esteban-andrade/AutonomousFireDataCollect/flir_one_node/demo/Screenshot from 2021-02-14 20-05-26.png

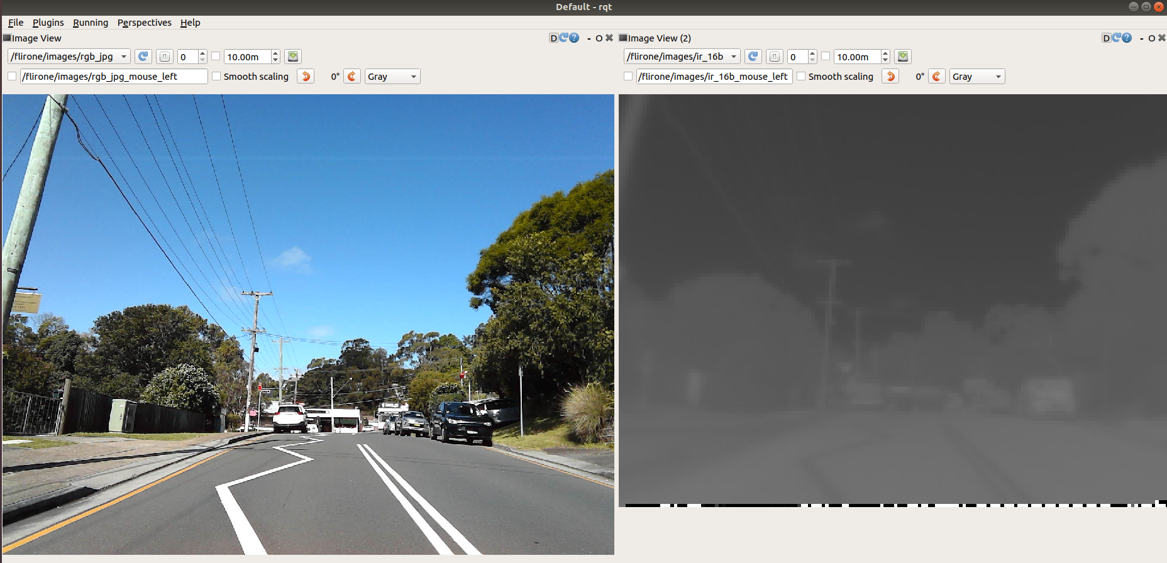
flir_one_node/demo/Screenshot from 2021-02-14 20-05-26.png
