esteban-andrade/AutonomousFireDataCollect/flir_one_node/demo/Screenshot from 2021-02-15 16-28-25.png

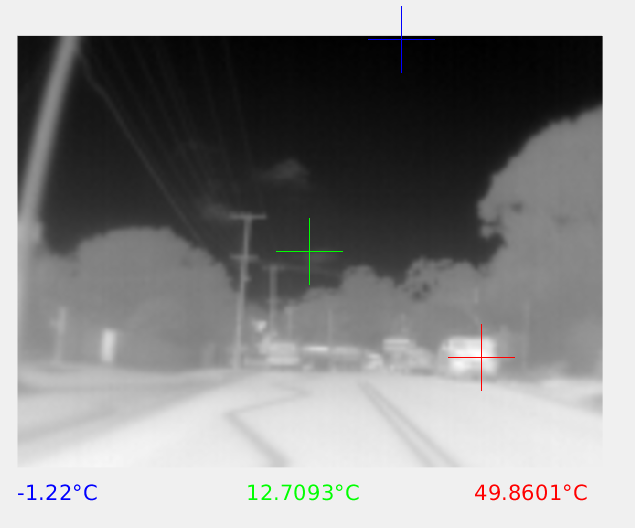
flir_one_node/demo/Screenshot from 2021-02-15 16-28-25.png
