esteban-andrade/AutonomousFireDataCollect/flir_one_node/demo/Screenshot from 2021-02-15 16-32-08.png

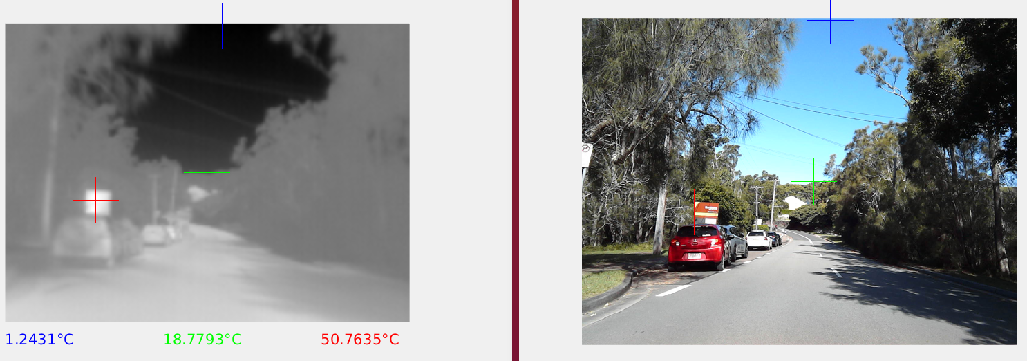
flir_one_node/demo/Screenshot from 2021-02-15 16-32-08.png
