esteban-andrade/AutonomousFireDataCollect/flir_one_node/demo/Screenshot from 2021-02-16 15-38-59.png

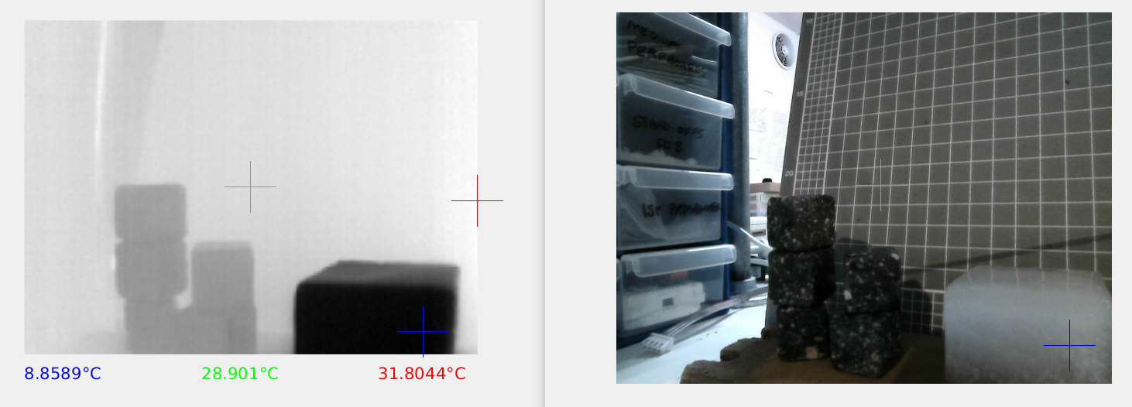
flir_one_node/demo/Screenshot from 2021-02-16 15-38-59.png
