esteban-andrade/AutonomousFireDataCollect/flir_one_node/demo/Screenshot from 2021-02-16 15-42-15.png

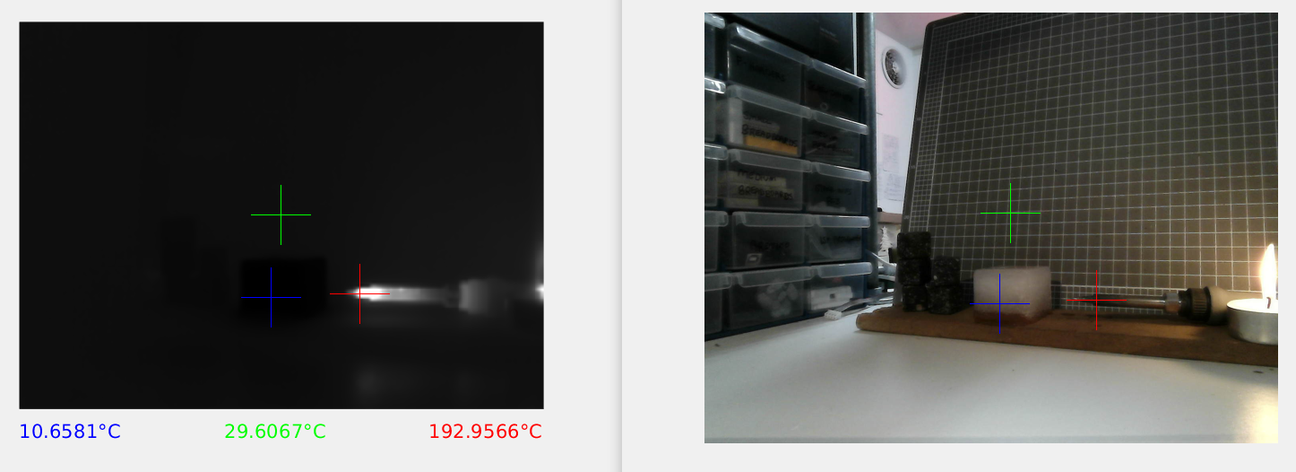
flir_one_node/demo/Screenshot from 2021-02-16 15-42-15.png
