esteban-andrade/AutonomousFireDataCollect/flir_one_node/demo/Screenshot from 2021-02-16 16-03-48.png

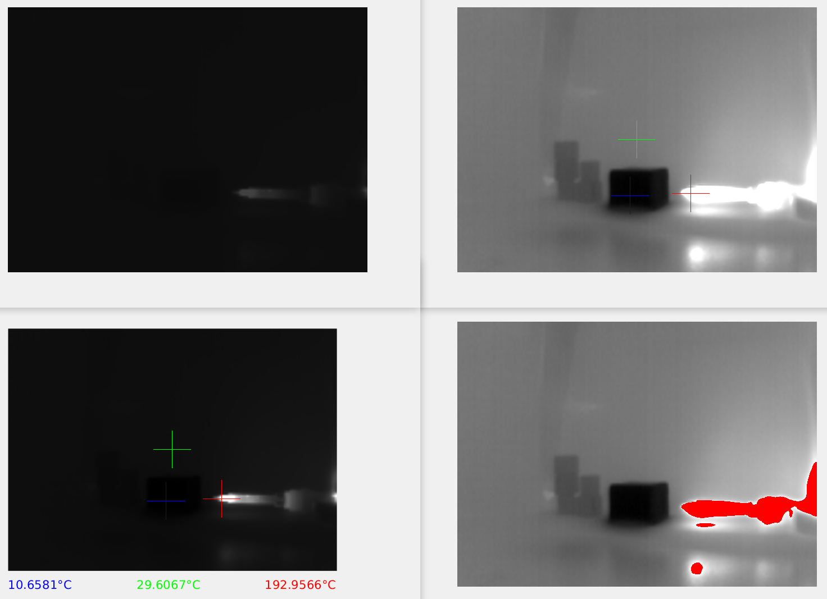
flir_one_node/demo/Screenshot from 2021-02-16 16-03-48.png
