esteban-andrade/AutonomousFireDataCollect/flir_one_node/v4l2loopback/new2.png

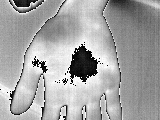
flir_one_node/v4l2loopback/new2.png
