esteban-andrade/AutonomousFireDataCollect/flir_one_node/v4l2loopback/new.png

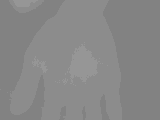
flir_one_node/v4l2loopback/new.png
