esteban-andrade/AutonomousFireDataCollect/flir_one_node/v4l2loopback/rgb.jpg

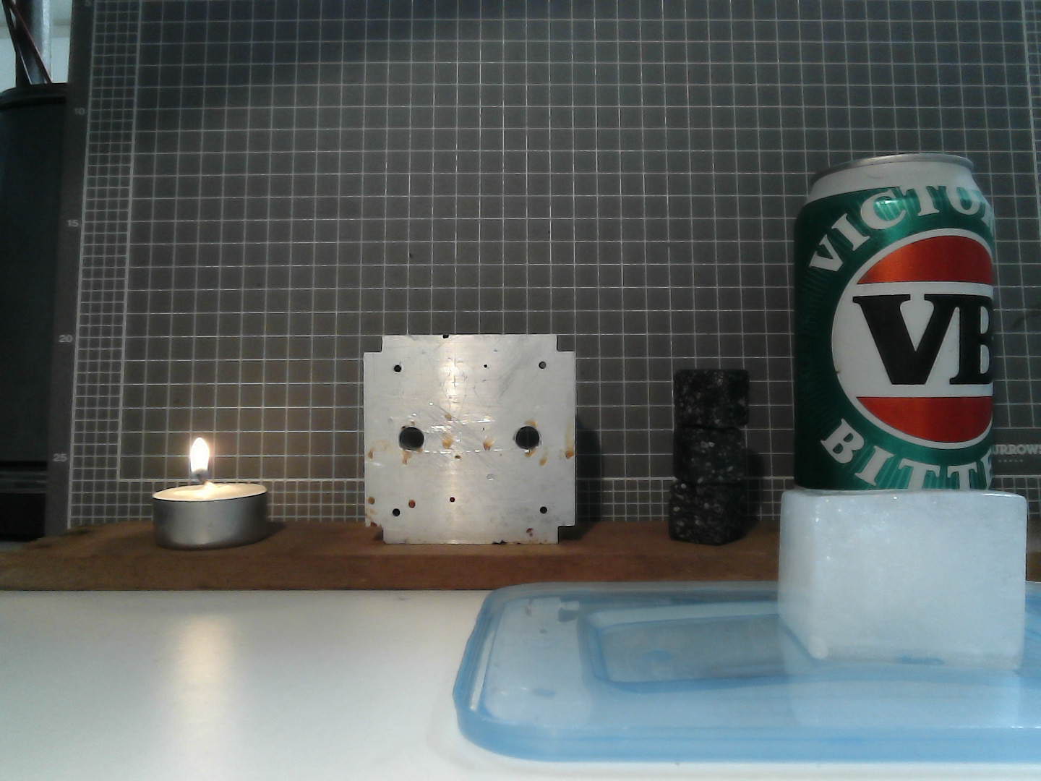
flir_one_node/v4l2loopback/rgb.jpg
